For-the-republic/VVFD/codebase/VFDmatrixFinder/src/lookup.cpp

#include "Arduino.h"
#include "acGeneratorVFD.h"
#include "wire.h"
#include "lookup.h"

// 5x7 Font Lookup Table (A–Z, 0–9)
// Each character = 7 rows of 5 bits, packed into bytes (lowest 5 bits used)
// 5x7 ASCII Font (0x20–0x7A)
// Each char = 7 bytes, each byte = 5-bit row (LSB = left pixel)

// 5x7 ASCII Font (0x20–0x7A)
// Each char = 7 bytes, each byte = 5-bit row (LSB = left pixel)

// 5x7 ASCII font packed into binary (SPACE → 'z')
// Each character is 35 bits stored in uint64_t
// Bit order: row by row, left to right
// Example: font5x7['3' - 0x20] = 0b00100010100001010010101001010011010ULL

const uint64_t font5x7[] = {
    0b00000000000000000000000000000000000ULL, // ' ' (0x20)
    0b00100001000010000100000000000100000ULL, // '!'
    0b01010010100101000000000000000000000ULL, // '"'
    0b01010011111010100111101010000000000ULL, // '#'
    0b00100011111000011111000010000000000ULL, // '$'
    0b11001011010001000101011001000000000ULL, // '%'
    0b01000101001010001001001010100000000ULL, // '&'
    0b00100001000010000000000000000000000ULL, // '''
    0b00010001000100001000010000010000000ULL, // '('
    0b01000001000010000100010001000000000ULL, // ')'
    0b00000010100111001110010100000000000ULL, // '*'
    0b00000001000010011111001000010000000ULL, // '+'
    0b00000000000000000000001000100010000ULL, // ','
    0b00000000000000011111000000000000000ULL, // '-'
    0b00000000000000000000001000100000000ULL, // '.'
    0b00001000100010001000100010000000000ULL, // '/'
    0b01110100011000110001100010111000000ULL, // '0'
    0b00100011000010000100001000111000000ULL, // '1'
    0b01110100010000100111010000111110000ULL, // '2'
    0b00100010100001010010101001010011010ULL, // '3'
    0b00010001100101011111001000010000000ULL, // '4'
    0b11111100001111000001000011111000000ULL, // '5'
    0b00111110000111110001000100111000000ULL, // '6'
    0b11111000010001000100010001000000000ULL, // '7'
    0b01110100010111010001000101110000000ULL, // '8'
    0b01110100010001011111000011110000000ULL, // '9'
    0b00000001000100000000010001000000000ULL, // ':'
    0b00000001000100000000010001000010000ULL, // ';'
    0b00010001001000010000100000010000000ULL, // '<'
    0b00000000011111000011111000000000000ULL, // '='
    0b01000000100000010010001000000000000ULL, // '>'
    0b01110100010000100110000000100000000ULL, // '?'
    0b01110100010111010111000101111000000ULL, // '@'
    0b00100010100010111111000100010000000ULL, // 'A'
    0b11110010010111001001010011110000000ULL, // 'B'
    0b01110100011000010000100010111000000ULL, // 'C'
    0b11110010010100101001010011110000000ULL, // 'D'
    0b11111100001110010000100011111000000ULL, // 'E'
    0b11111100001110010000100010000000000ULL, // 'F'
    0b01110100011000010111100010111000000ULL, // 'G'
    0b10001100011111110001100011000100000ULL, // 'H'
    0b01110001000010000100001000111000000ULL, // 'I'
    0b00111000100001000010001000110000000ULL, // 'J'
    0b10001100101110010010100011000100000ULL, // 'K'
    0b10000100001000010000100001111100000ULL, // 'L'
    0b10001110111010110001100011000100000ULL, // 'M'
    0b10001110011010110011100011000100000ULL, // 'N'
    0b01110100011000110001100010111000000ULL, // 'O'
    0b11110100011000111110100001000000000ULL, // 'P'
    0b01110100011000110101100100110100000ULL, // 'Q'
    0b11110100011000111110101001000100000ULL, // 'R'
    0b01111100000111000001000011111000000ULL, // 'S'
    0b11111001000010000100001000010000000ULL, // 'T'
    0b10001100011000110001100010111000000ULL, // 'U'
    0b10001100011000101010010100010000000ULL, // 'V'
    0b10001100011000110101101011101100000ULL, // 'W'
    0b10001100010101000100010101000100000ULL, // 'X'
    0b10001010101000100001000010001000000ULL, // 'Y'
    0b11111000010001000100010001111100000ULL, // 'Z'
    0b01110010000100001000010000111000000ULL, // '['
    0b10000100001000010000100001000010000ULL, // '\'
    0b01110000100001000010000100111000000ULL, // ']'
    0b00100010101000100000000000000000000ULL, // '^'
    0b00000000000000000000000001111100000ULL, // '_'
    0b00100001000010000000000000000000000ULL, // '`'
    0b00000000000111000001011110011100000ULL, // 'a'
    0b10000100001111010001100011110000000ULL, // 'b'
    0b00000000000111010000100010111000000ULL, // 'c'
    0b00001000010111010001100010111000000ULL, // 'd'
    0b00000000000111010001111110111000000ULL, // 'e'
    0b00110010010110001000010000111000000ULL, // 'f'
    0b00000000000111110001111100000111110ULL, // 'g'
    0b10000100001111010001100011000100000ULL, // 'h'
    0b00100000000110000100001000111000000ULL, // 'i'
    0b00010000000011000010001000100011100ULL, // 'j'
    0b10000100001010011000101001000100000ULL, // 'k'
    0b01100001000010000100001000111000000ULL, // 'l'
    0b00000000001101010101101011010100000ULL, // 'm'
    0b00000000001111010001100011000100000ULL, // 'n'
    0b00000000000111010001100010111000000ULL, // 'o'
    0b00000000001111010001111101000010000ULL, // 'p'
    0b00000000000111010001111100000100001ULL, // 'q'
    0b00000000001011011000010000111000000ULL, // 'r'
    0b00000000000111110000011110011100000ULL, // 's'
    0b00100001000111100010000100001100000ULL, // 't'
    0b00000000001000110001100010111000000ULL, // 'u'
    0b00000000001000110001101010001000000ULL, // 'v'
    0b00000000001000110001101011101100000ULL, // 'w'
    0b00000000001000101010001001000100000ULL, // 'x'
    0b00000000001000110001111100000111110ULL, // 'y'
    0b00000000001111100010010001011111000ULL, // 'z'
};


lookupTable::lookupTable()
{

}
uint8_t lookupTable:: Lookup(char letter){
    //48 is the starting position of 0 in ascii
    return font5x7[32 - letter];    
    }
