For-the-republic/VVFD/codebase/VFDmatrixFinder/src/lookup.h

#ifndef LOOKUP_H
#define LOOKUP_H

#include "Arduino.h"
#include "acGeneratorVFD.h"
#include "wire.h"
class lookupTable {
    public:
    lookupTable();
    uint8_t Lookup(char letter);
    private:
};
#endif
